ide/usb-c-to-c-power-mod/USB-C-to-C Power Mod.sch

## KiCad design USB-C-to-C Power Mod.sch (2021-05-16)

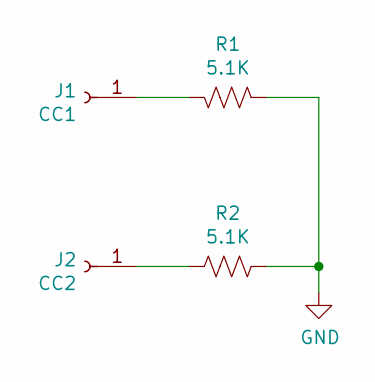
[picture p9: schematic USB-C-to-C Power Mod.sch]

Parts:
J1: CC1; Plated_Hole_D0.3mm
J2: CC2; Plated_Hole_D0.3mm
R1, R2: 5.1K; R_0402_1005Metric

Connections:
GND: R1.2, R2.1
unnamed: J1.1, R1.1
unnamed: J2.1, R2.2
